IiroKarppanen/smartwatch/Software/assets/image_fx_abstract_white_lines_over_black_background (2).jpg

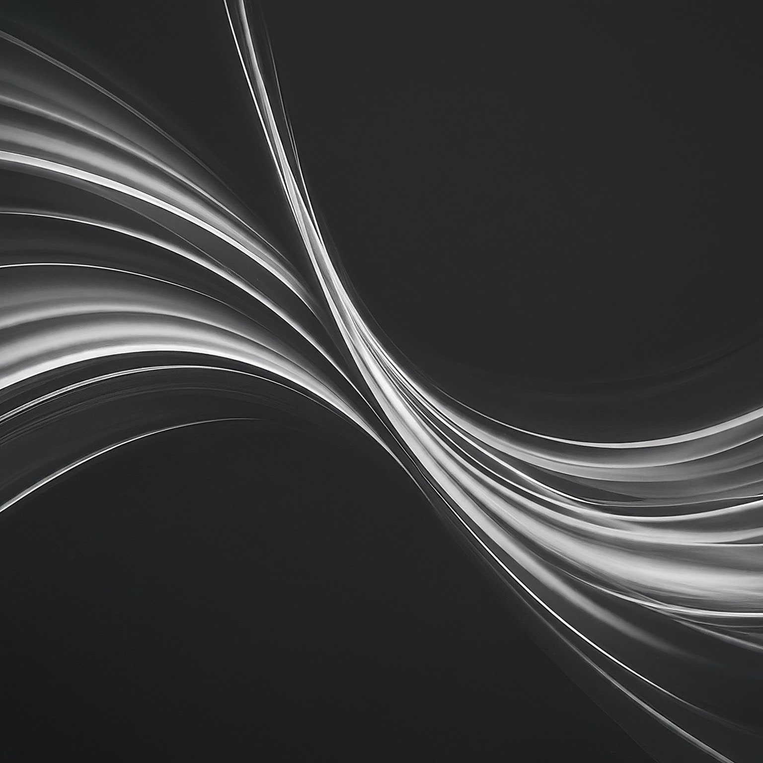
Software/assets/image_fx_abstract_white_lines_over_black_background (2).jpg
